davegutz/ESC/documentation/2016-10-14 04.49.10.jpg

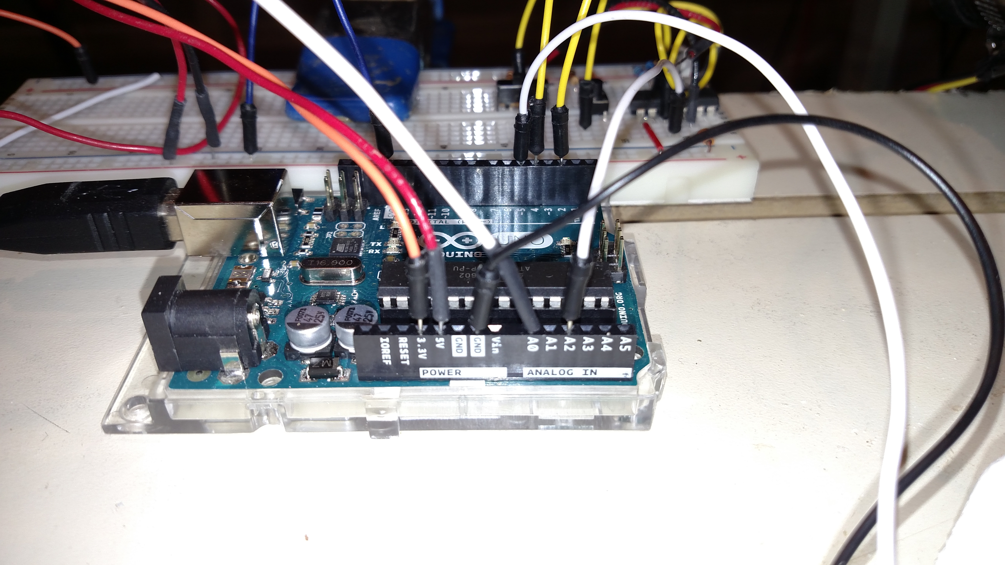
documentation/2016-10-14 04.49.10.jpg
