davegutz/ESC/documentation/2016-10-14 04.49.18.jpg

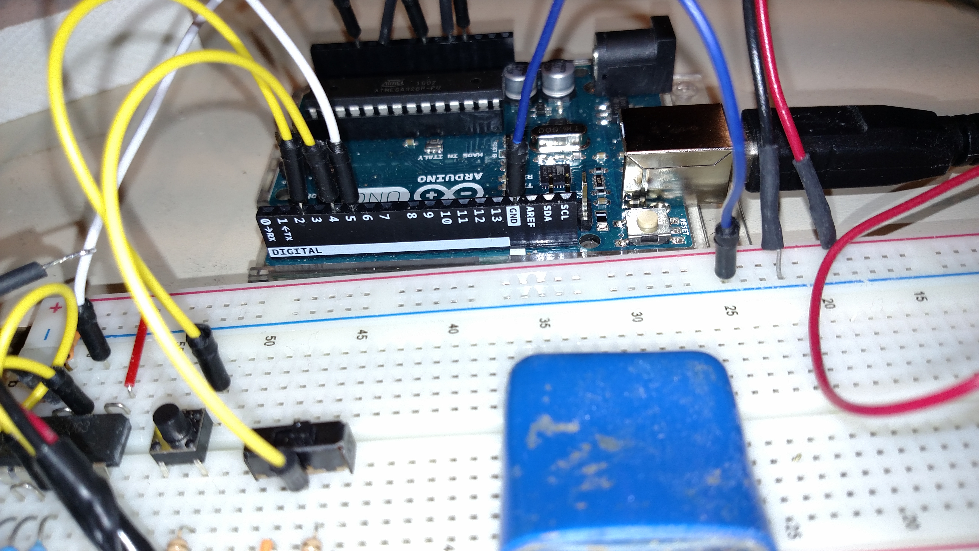
documentation/2016-10-14 04.49.18.jpg
