davegutz/ESC/documentation/2016-12-07 10.25.46.jpg

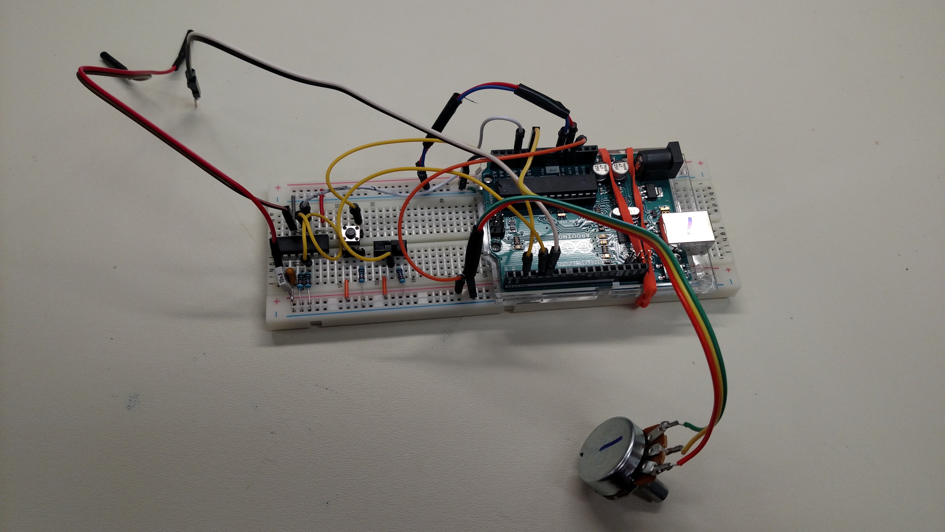
documentation/2016-12-07 10.25.46.jpg
