davegutz/ESC/documentation/2016-12-07 10.25.56.jpg

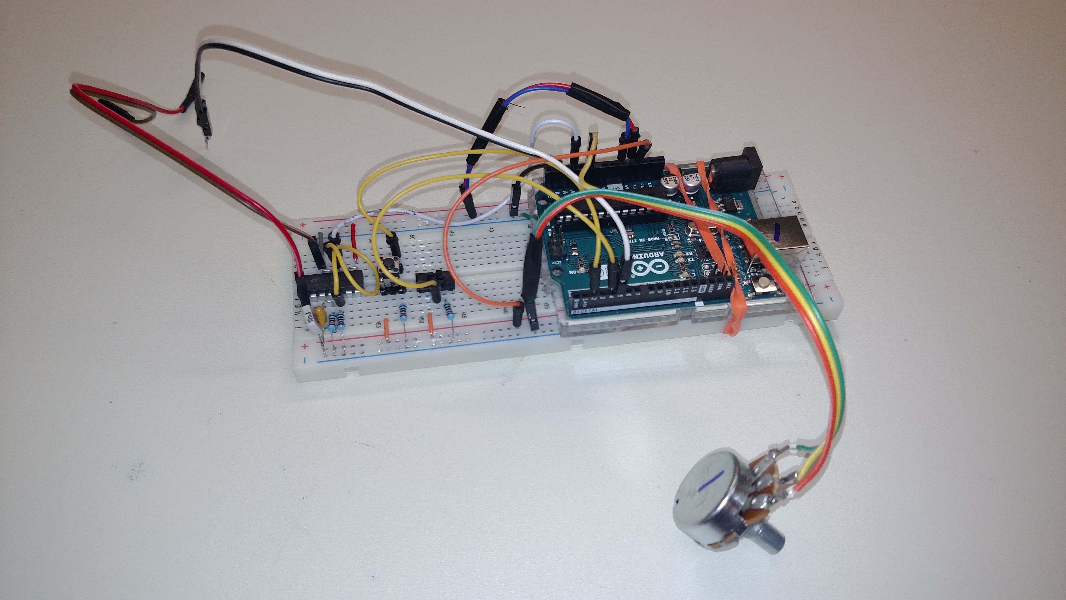
documentation/2016-12-07 10.25.56.jpg
