davegutz/ESC/documentation/arduinoWind_bb.png

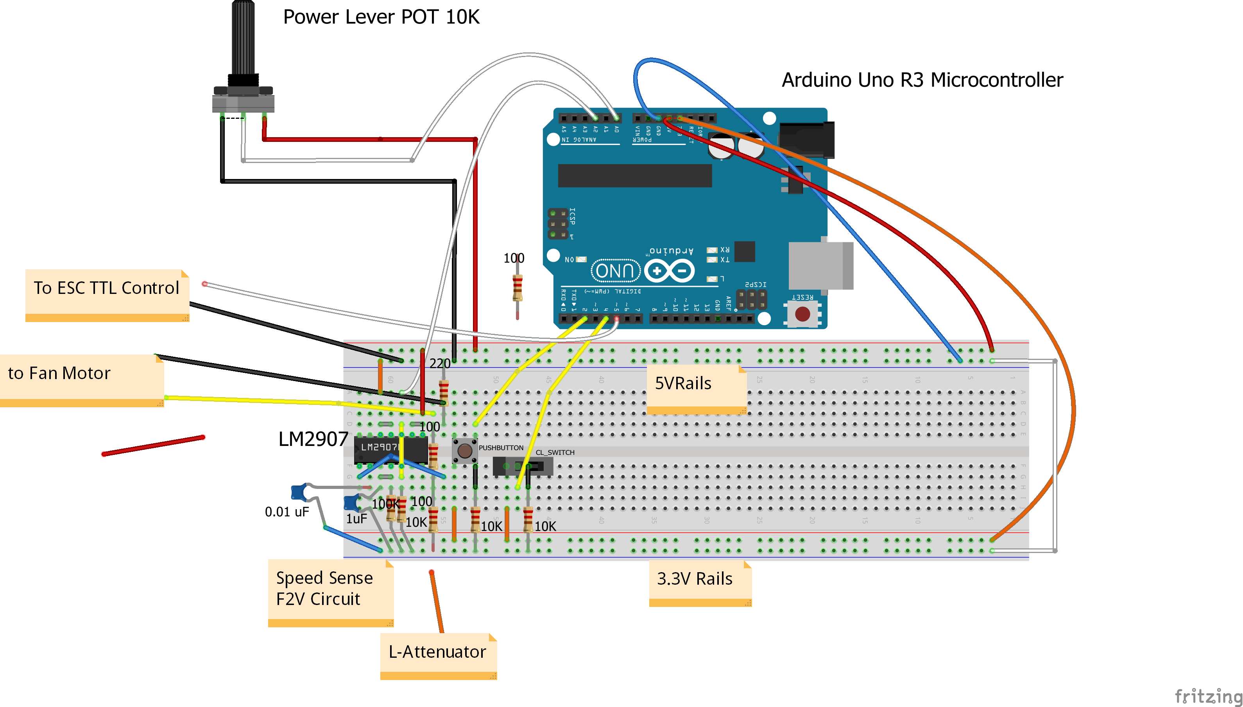
documentation/arduinoWind_bb.png
