davegutz/ESC/documentation/massOfRotor.jpg

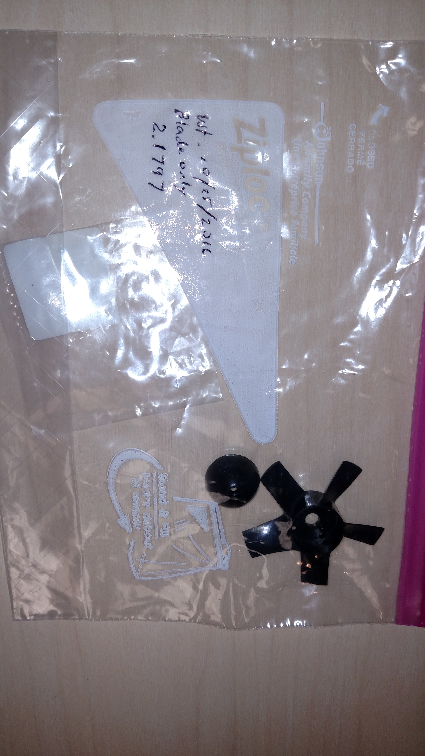
documentation/massOfRotor.jpg
