davegutz/ESC/documentation/photonESC_bb.png

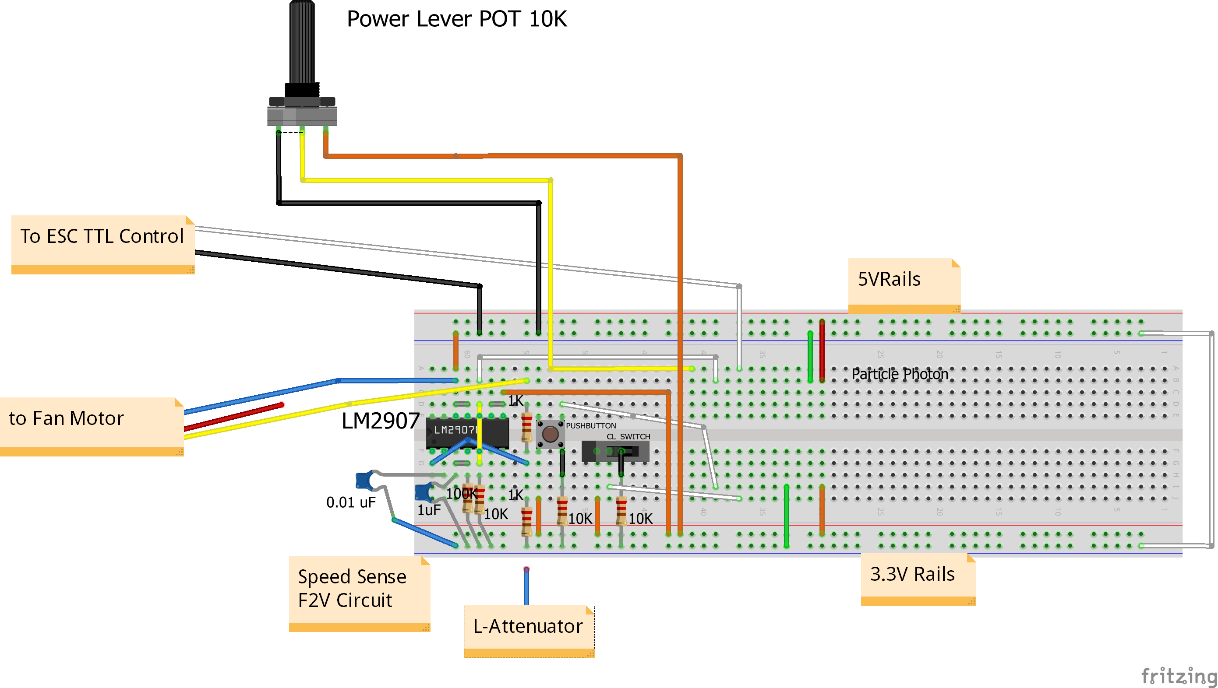
documentation/photonESC_bb.png
