davegutz/ESC/documentation/photonWind_wind.png

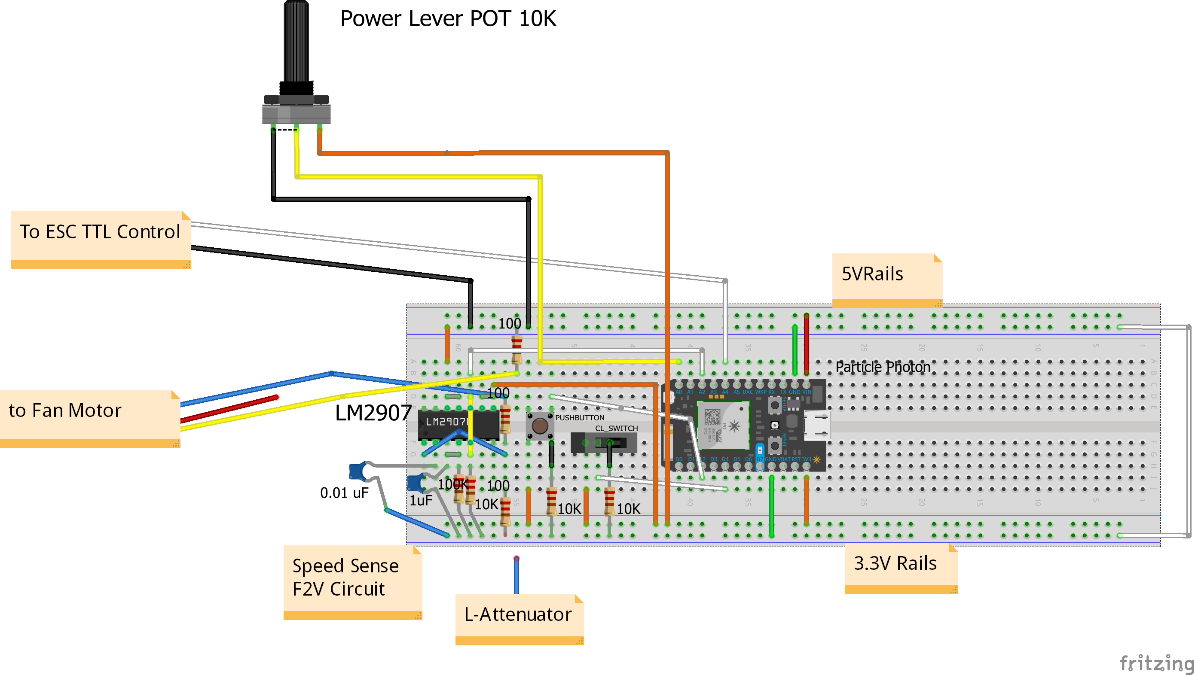
documentation/photonWind_wind.png
