davegutz/ESC/myESC-Particle-DEV/saves/2016-08-15 15.57.37.jpg

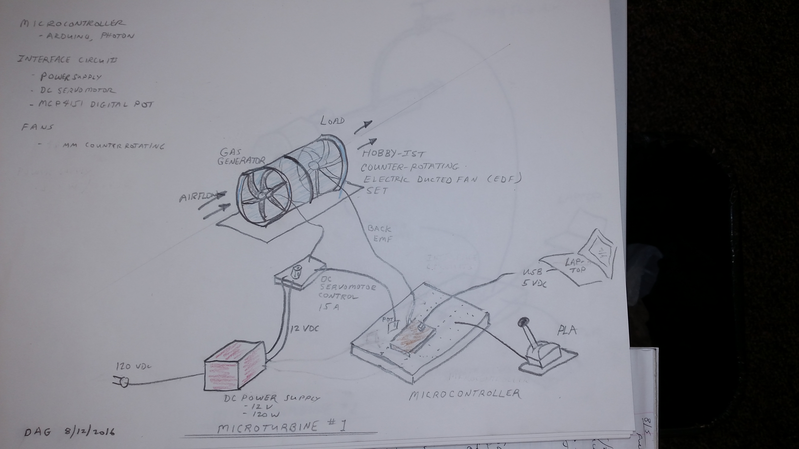
myESC-Particle-DEV/saves/2016-08-15 15.57.37.jpg
