davegutz/ESC/myESC-Particle-DEV/saves/2016-09-13 07.13.25.jpg

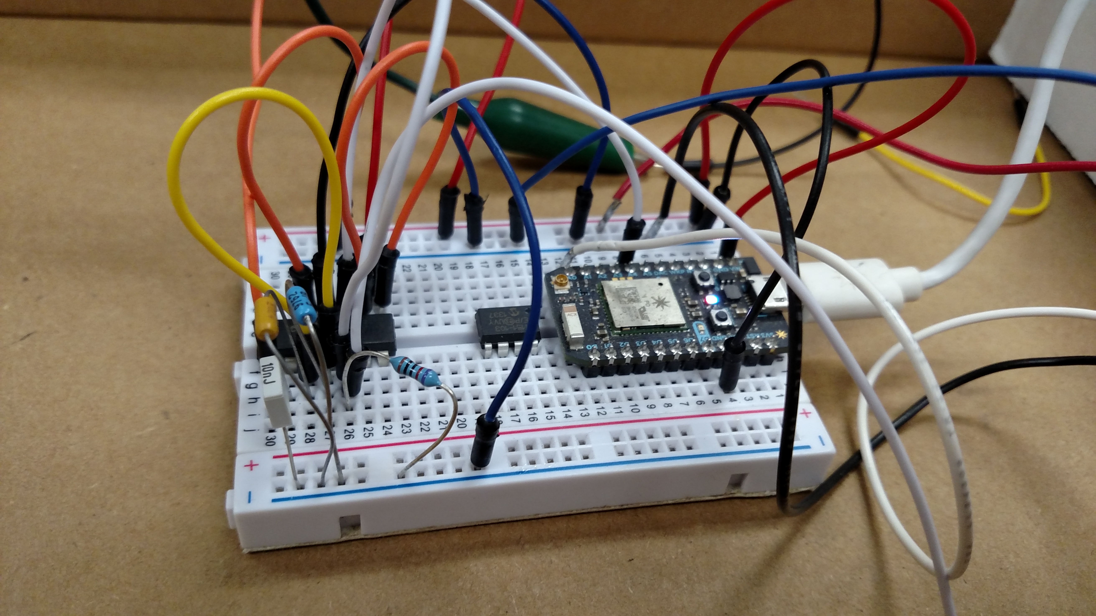
myESC-Particle-DEV/saves/2016-09-13 07.13.25.jpg
