davegutz/ESC/myESC-Particle-DEV/saves/2016-09-13 07.13.37.jpg

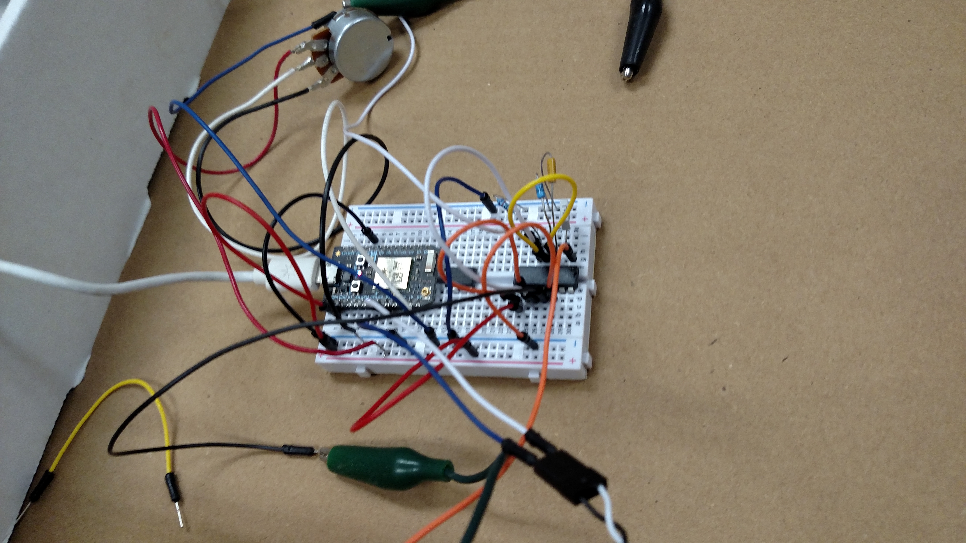
myESC-Particle-DEV/saves/2016-09-13 07.13.37.jpg
