davegutz/ESC/myESC-Particle-DEV/saves/2016-09-15 16.05.50.jpg

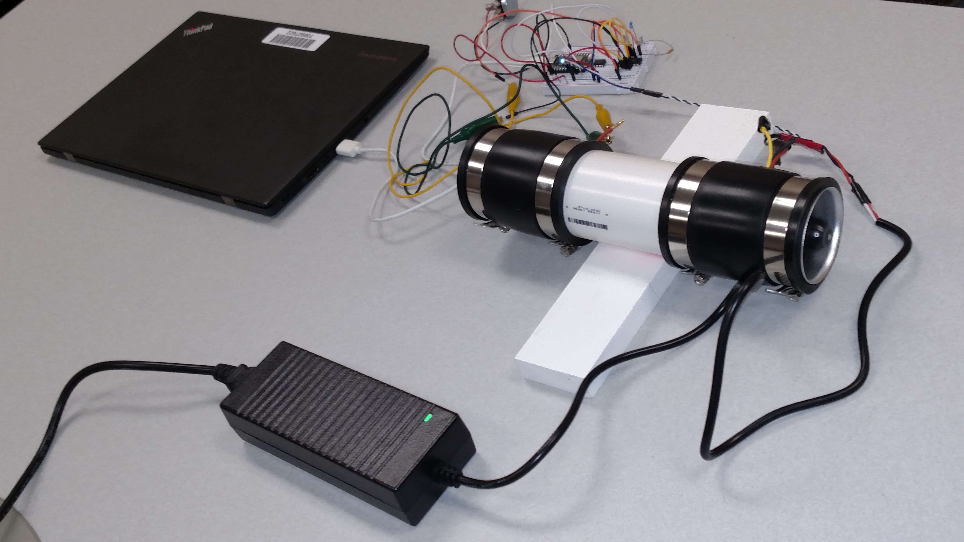
myESC-Particle-DEV/saves/2016-09-15 16.05.50.jpg
