davegutz/ESC/myESC-Particle-DEV/saves/2016-09-15 16.06.02.jpg

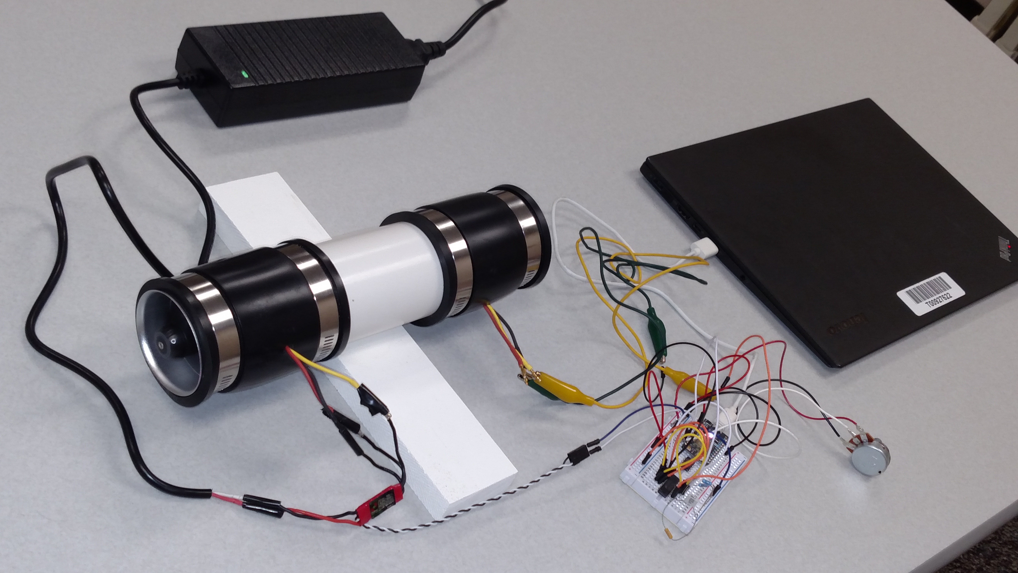
myESC-Particle-DEV/saves/2016-09-15 16.06.02.jpg
