davegutz/ESC/Problem/2016-10-06 06.58.44.jpg

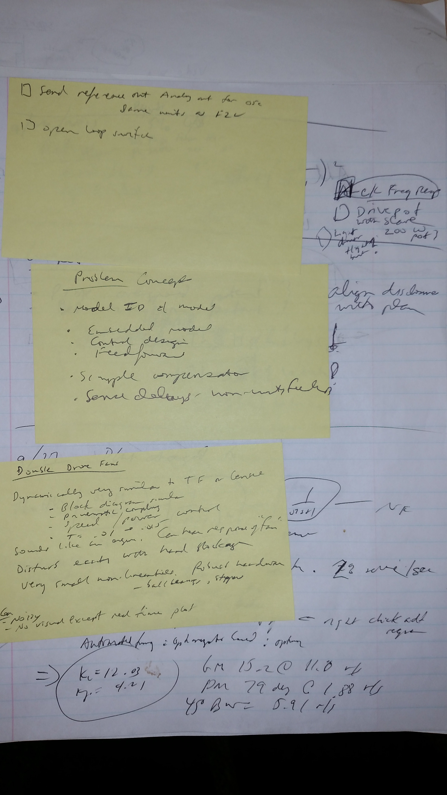
Problem/2016-10-06 06.58.44.jpg
