davegutz/ESC/Problem/2016-10-12 15.18.13.jpg

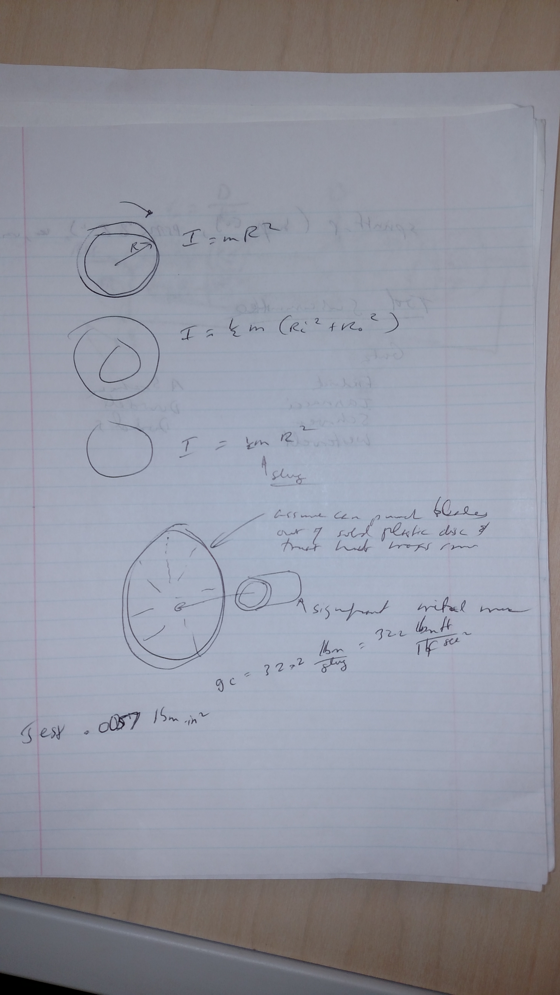
Problem/2016-10-12 15.18.13.jpg
