davegutz/ESC/Problem/2016-10-17 14.30.32.jpg

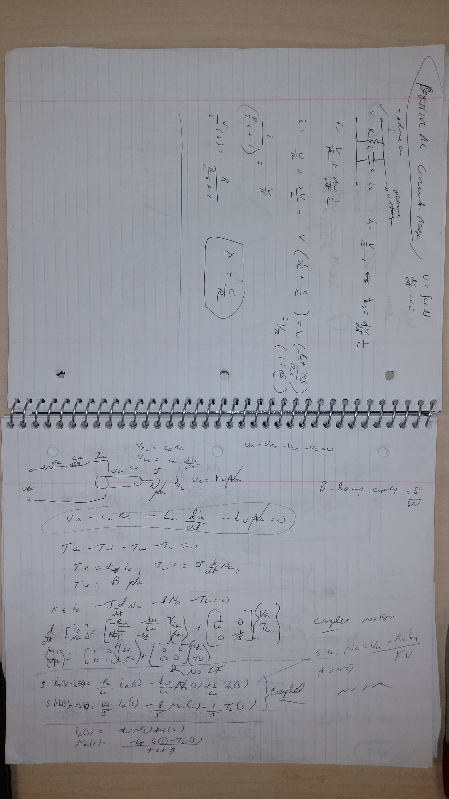
Problem/2016-10-17 14.30.32.jpg
