davegutz/ESC/Problem/2016-10-26 18.43.36.jpg

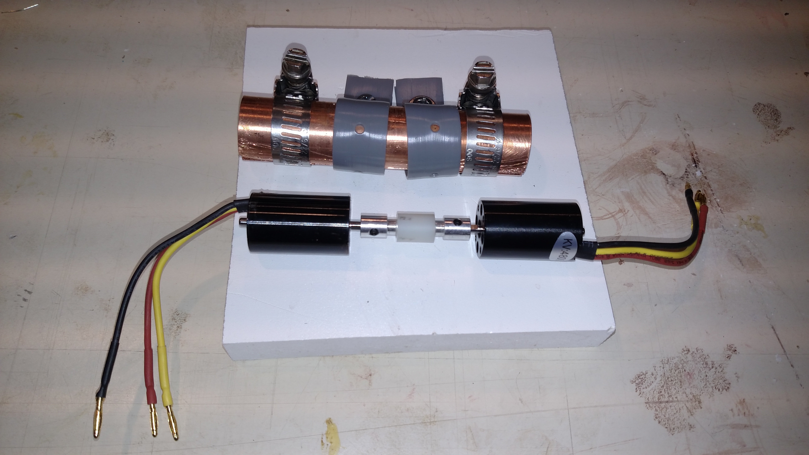
Problem/2016-10-26 18.43.36.jpg
