davegutz/ESC/Problem/2016-11-22 20.52.22.jpg

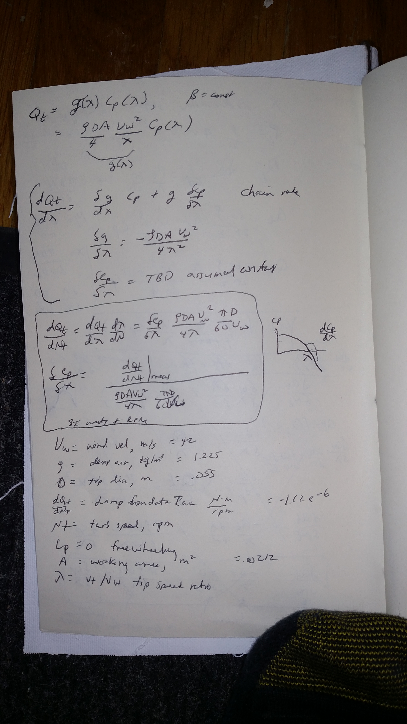
Problem/2016-11-22 20.52.22.jpg
