davegutz/ESC/documentation/Frequency Response _draw_io.pdf

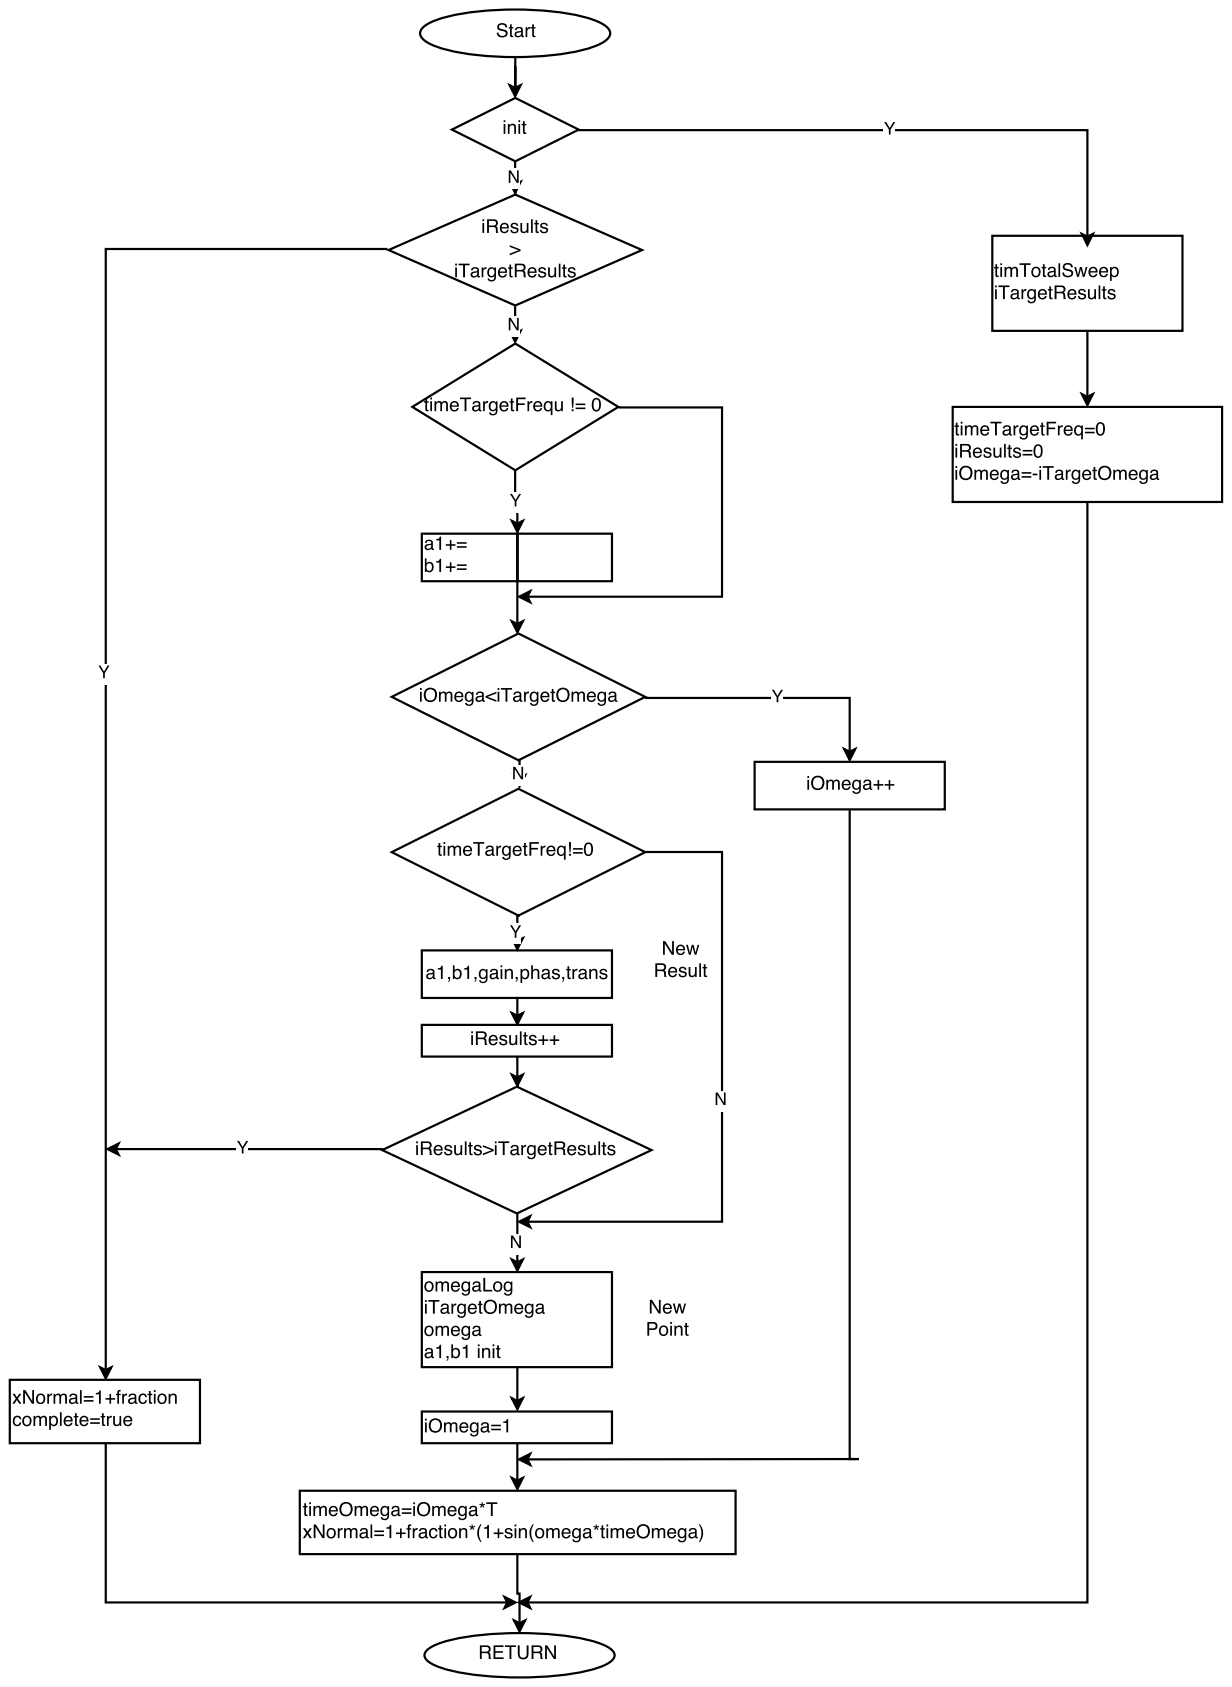
[picture p57: page 1]
