davegutz/ESC/circuits/LM2907-LM2917/LM2907-8 test.asc

C1: cap; 10nF
C2: cap; .1µF
C3: cap; .1µF
C4: cap; 10µF
C5: cap; .1µF
D1: zener; 1N755
R1: res; 47k
R2: res; 10k
R3: res; 100k
Rzener: res; 470
U1: LM2907-8
V1: voltage; 14; Rser=0.3
V2: voltage; SINE(0 .1 .4k)
Named nets: 0, Vcc, +in, c1ext, c2ext, Out, Out2
.tran 0 100m 0 10u startup
