davegutz/ESC/circuits/LM2907-LM2917/LM2907-14 myESC.asc

C1: cap; 10nF
C2: cap; 1µF
R1: res; 100k
R5: res; 10k
U1: LM2907-14
V1: voltage; 5; Rser=0.3
V2: voltage; SINE(0 8 .4k); AC 8 0
Named nets: 0, c1ext, c2ext, Out, Vin, Vout
;tran 0 2000m 0 10u
