davegutz/ESC/documentation/2016-10-14 03.43.12.jpg

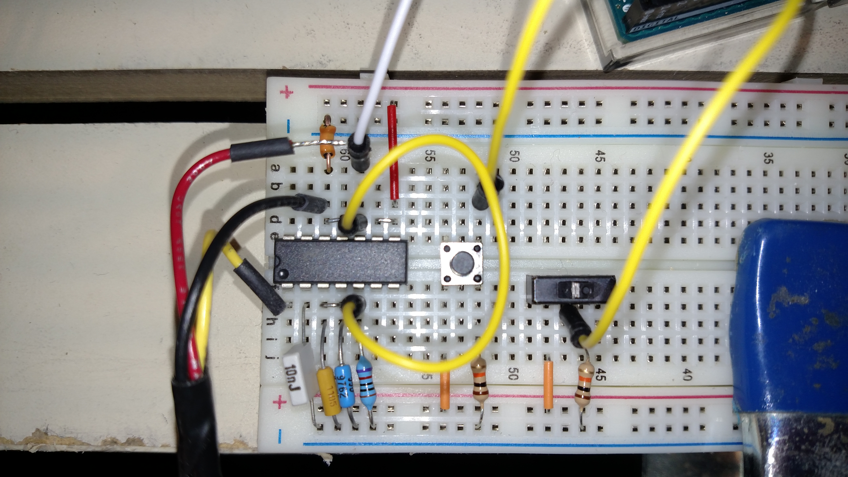
documentation/2016-10-14 03.43.12.jpg
