davegutz/ESC/Problem/2016-11-22 20.51.25.jpg

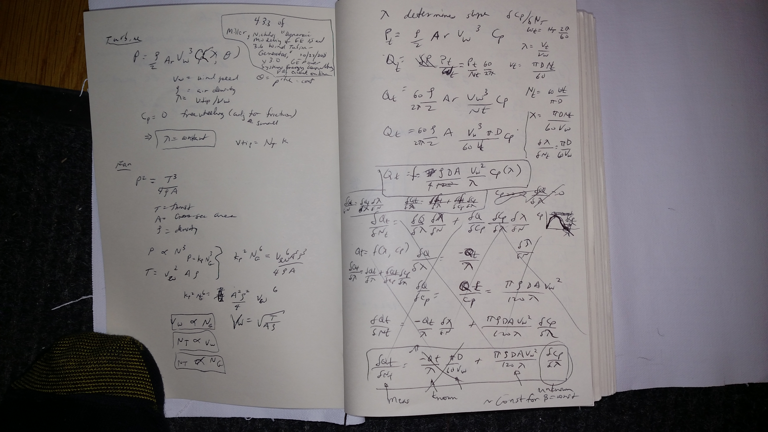
Problem/2016-11-22 20.51.25.jpg
